tops4u/Ram-Tester/Docs/Archive/legacy/LED signals-2.pdf

### LED signals explained (Version 2.3.0 and later)

System test mode active check documentation

Test successful – Tested larger type by pin numbers

Test successful – Tested smaller type by pin numbers

Test successful – Tested larger Static Column type

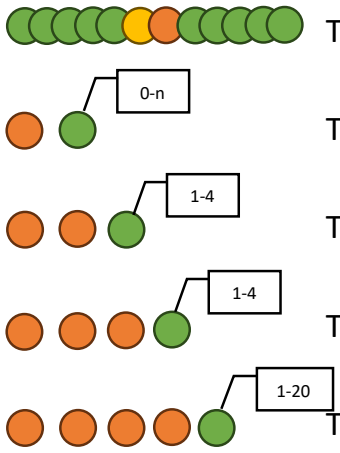
[picture p28: figure]

Test successful – Tested smaller Static Colmun type

Test failed – Address decoder Nr. greens = address line

Test failed – Memory cell test. Nr. greens = Test pattern

Test failed – Row crosstalk or data retention fail

Test failed – Ground short on pin nr of green blinks

Fast red only – Config error (check DIP switches)

Test running – please wait takes up to 10sec
