tops4u/Ram-Tester/Media/Retention_End.jpg

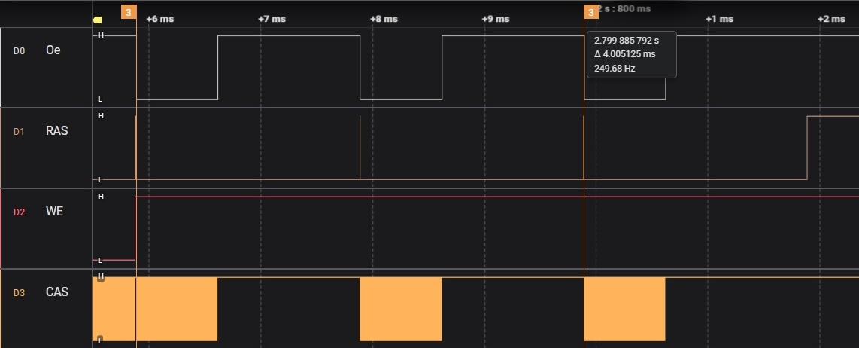
Media/Retention_End.jpg
