tops4u/Ram-Tester/Schematic/4116/4116.JPG

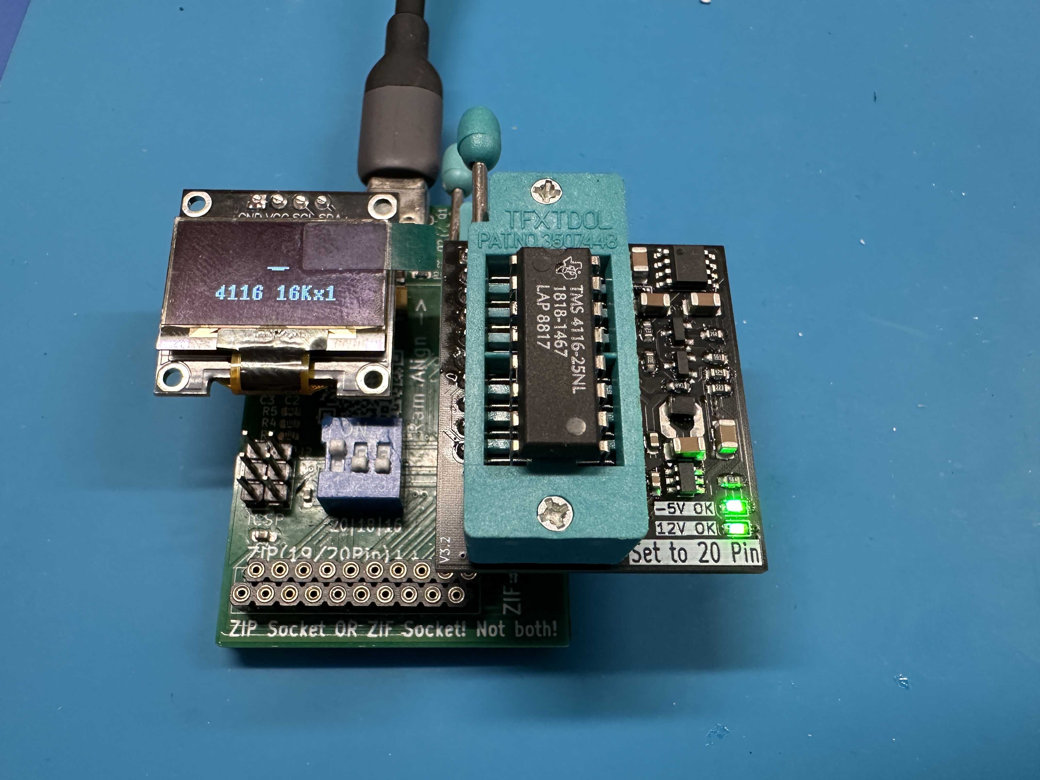
Schematic/4116/4116.JPG
