tops4u/Ram-Tester/Docs/Measurements/1stGen_ShortTest.bmp

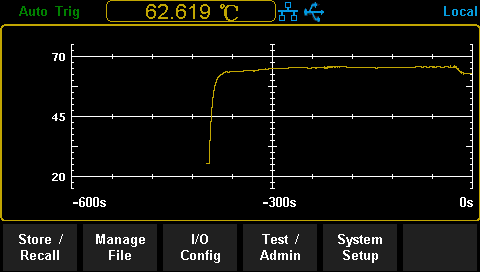
Docs/Measurements/1stGen_ShortTest.bmp
