tops4u/Ram-Tester/Docs/Measurements/3rdGen_ShortTest.bmp

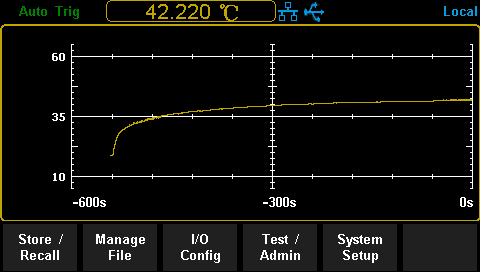
Docs/Measurements/3rdGen_ShortTest.bmp
