tops4u/Ram-Tester/Docs/Measurements/4116_-5V.png

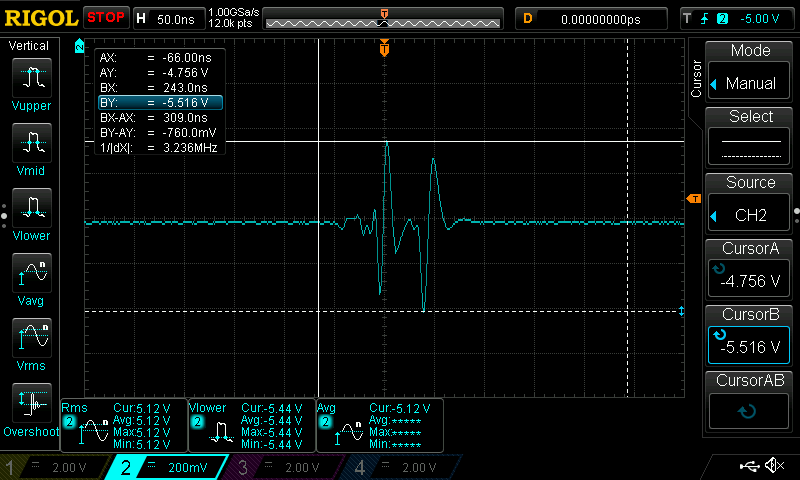
Docs/Measurements/4116_-5V.png
