tops4u/Ram-Tester/Docs/Measurements/4116_Dataline.png

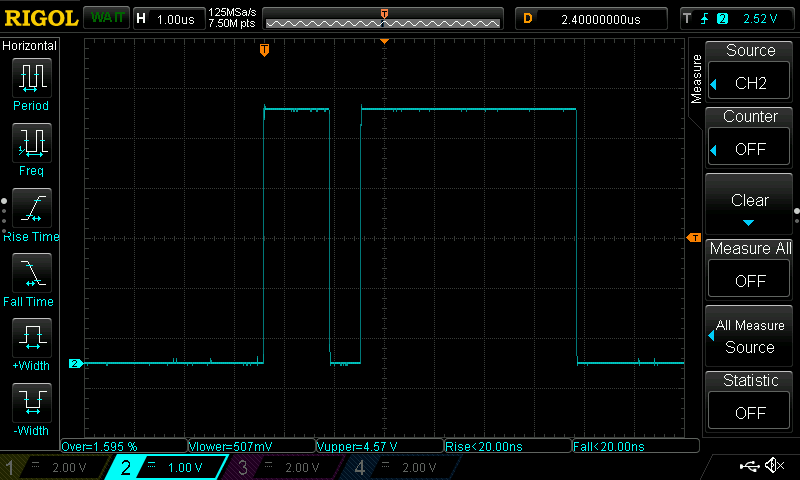
Docs/Measurements/4116_Dataline.png
