tops4u/Ram-Tester/Docs/Measurements/514400_CAS.png

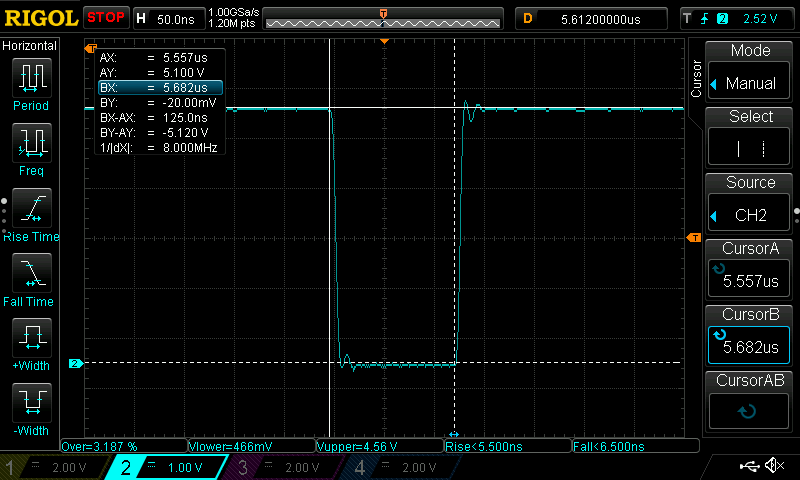
Docs/Measurements/514400_CAS.png
