tops4u/Ram-Tester/Schematic/TH/Archive/Schematic_TH.pdf

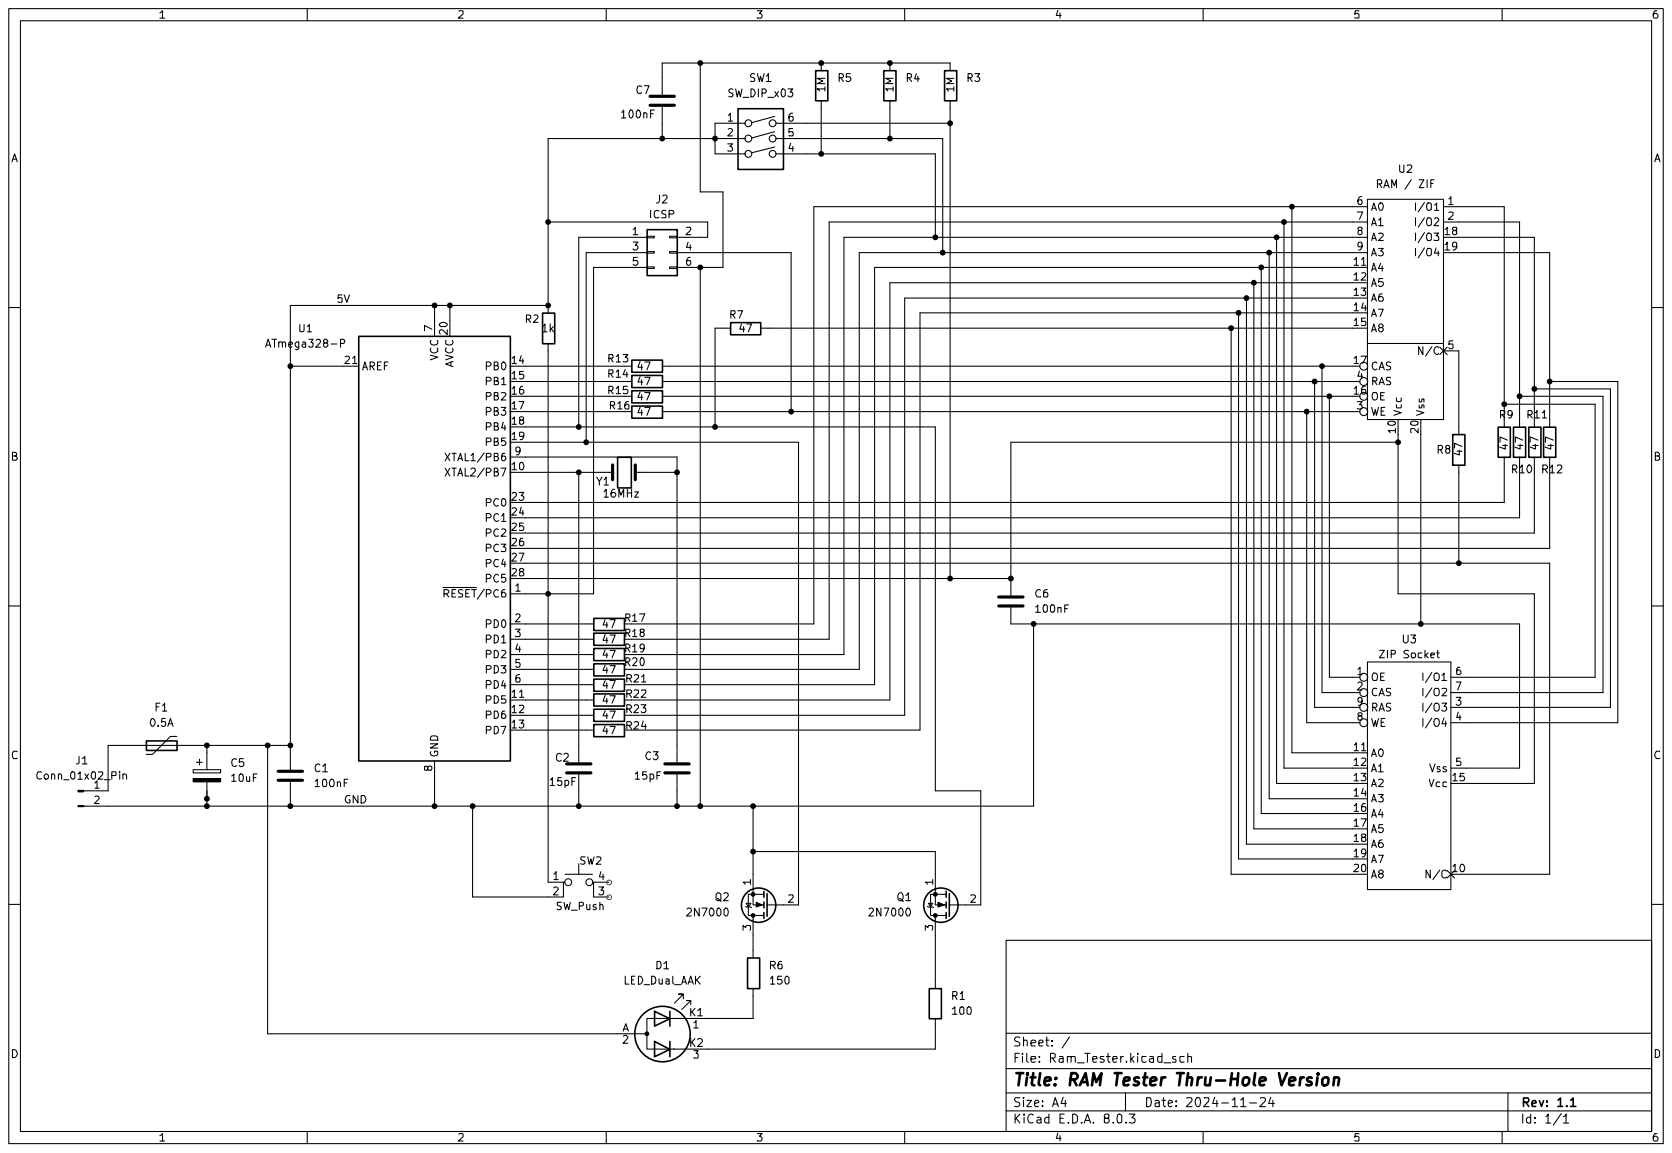
[picture p51: page 1]
